spectrumero/filestick/system/console.c

/*
;The MIT License
;
;Copyright (c) 2023 Dylan Smith
;
;Permission is hereby granted, free of charge, to any person obtaining a copy
;of this software and associated documentation files (the "Software"), to deal
;in the Software without restriction, including without limitation the rights
;to use, copy, modify, merge, publish, distribute, sublicense, and/or sell
;copies of the Software, and to permit persons to whom the Software is
;furnished to do so, subject to the following conditions:
;
;The above copyright notice and this permission notice shall be included in
;all copies or substantial portions of the Software.
;
;THE SOFTWARE IS PROVIDED "AS IS", WITHOUT WARRANTY OF ANY KIND, EXPRESS OR
;IMPLIED, INCLUDING BUT NOT LIMITED TO THE WARRANTIES OF MERCHANTABILITY,
;FITNESS FOR A PARTICULAR PURPOSE AND NONINFRINGEMENT. IN NO EVENT SHALL THE
;AUTHORS OR COPYRIGHT HOLDERS BE LIABLE FOR ANY CLAIM, DAMAGES OR OTHER
;LIABILITY, WHETHER IN AN ACTION OF CONTRACT, TORT OR OTHERWISE, ARISING FROM,
;OUT OF OR IN CONNECTION WITH THE SOFTWARE OR THE USE OR OTHER DEALINGS IN
;THE SOFTWARE.
*/

#include <stdint.h>
#include <stdbool.h>
#include <unistd.h>
#include <sys/stat.h>
#include <string.h>
#include <sys/errno.h>

#include "sys/console.h"
#include "console.h"
#include "fd.h"
#include "sysdefs.h"
#include "devices.h"

static FDfunction cons_func = {
   .fd_read  = console_read,
   .fd_write = console_write,
   .fd_lseek = NULL,
   .fd_fstat = console_fstat,
   .fd_close = NULL,
   .fd_ioctl = console_ioctl,
   .fd_peek  = console_peek
};

#ifdef SOFTWARE_FIFO
extern volatile uint32_t bufindex;
extern volatile uint32_t bufstart;
extern volatile uint32_t cr_index;
extern volatile uint32_t cons_rx_count;
extern volatile uint32_t cons_control;

// This should be able to pick up the symbol, but it doesn't
uint8_t *cons_buf = (uint8_t *)0xff00; // FIXME system.ld symbol
#else
uint32_t       cons_control;
#endif

static ssize_t console_read_interactive(int fd, void *buf, size_t count);
static ssize_t console_read_raw(int fd, void *buf, size_t count);

//------------------------------------------------------------------
// Open the console
int open_console(const char *devname, int flags, mode_t mode, FD *fd) {
   fd->fdfunc = &cons_func;
   return 0;
}

//-----------------------------------------------------------------
// Read the console
ssize_t console_read(int fd, void *buf, size_t count) {
   if(cons_control & CONSOLE_RAW) 
      return console_read_raw(fd, buf, count);
   else 
      return console_read_interactive(fd, buf, count);
}

#ifdef SOFTWARE_FIFO
//-----------------------------------------------------------------
// Read the console in raw mode
static ssize_t console_read_raw(int fd, void *buf, size_t count)
{
   size_t bytes_remain = count;
   uint8_t *bufptr = (uint8_t *)buf;
   bool do_flow_control = false;

   if(!count) return 0;

   while(bytes_remain) {
      while(bufstart != bufindex && bytes_remain) {
         uint8_t byte = *(cons_buf + (bufstart & 0xFF));
         *bufptr++ = byte;

         bufstart++;
         bytes_remain--;
         do_flow_control = true;
      }

      if(do_flow_control) {
         if(cons_control & CONSOLE_FLOW_XOFF)
            serial_putc(FLOW_XON);

         do_flow_control = false;
      }
   }

   return count;
}

//-----------------------------------------------------------------
// Read the console in interactive mode (characters echoed, CR = end
// of transmission)
static ssize_t console_read_interactive(int fd, void *buf, size_t count)
{
   size_t bytes_read = 0;
   uint8_t *bufptr = (uint8_t *)buf;

   if(!count) return 0;

   // FIXME will need a way to break out (eg Ctrl-C)
   while(cons_rx_count == 0);

   DISABLE_INTERRUPTS
   cons_rx_count--;
   ENABLE_INTERRUPTS

   while(count && bufstart != bufindex) {
      // add the wrapped value of bufstart to get the buffer index
      uint8_t byte = *(cons_buf + (bufstart & 0xFF));
      *bufptr++ = byte;

      bufstart++;
      count--;
      bytes_read++;

   }

   return bytes_read;
}
#else // SOFTWARE_FIFO

// Using the hardware FIFO
volatile uint8_t  *uart_byte  = (uint8_t *)(DEV_BASE + OFFS_UART);
volatile uint32_t *uart_state = (uint32_t *)(DEV_BASE + OFFS_UARTSTATE);

//-----------------------------------------------------------------
// Read the console in raw mode
static ssize_t console_read_raw(int fd, void *buf, size_t count)
{
   uint8_t *bufptr = buf;
   ssize_t bytes_read = 0;

   while(count) {
      // wait for data
      while((*uart_state & 1) == 0);

      uint8_t byte = *uart_byte;
      *bufptr++ = byte;
      count--;
      bytes_read++;
   }
      
   return bytes_read;
}

//-----------------------------------------------------------------
// Read the console in interactive mode (characters echoed, CR = end
// of transmission)
static ssize_t console_read_interactive(int fd, void *buf, size_t count)
{
   size_t bytes_read = 0;
   uint8_t *bufptr = buf;
   if(count == 0) return 0;

   while(count) {
      // wait for data
      while((*uart_state & 1) == 0);

      uint8_t byte = *uart_byte;

      // CR
      if(byte == 0x0d) {
         serial_putc(0x0a);
         serial_putc(0x0d);
         break;
      }
      // backspace
      else if(byte == 127 || byte == 8) {
         if(bufptr > (uint8_t *)buf) {
            bufptr--;
            *bufptr = 0;
            bytes_read--;
            count++;
            serial_putc(8);
            serial_putc(' ');
            serial_putc(8);
         }
         else {
            // bell
            serial_putc(7);
         }
      }
      else {
         serial_putc(byte);
         count--;
         bytes_read++;
         *bufptr++ = byte;
      }
   }

   return bytes_read;
}
#endif

//------------------------------------------------------------------
// Return the number of bytes available
ssize_t console_peek(int fd) {
#ifdef SOFTWARE_FIFO
   return bufindex - bufstart;
#else
   // FIFO remaining bytes are in the upper 16 bits of the state
   // register
   return (*uart_state) >> 16;
#endif
}

//------------------------------------------------------------------
// Write to the system console.
ssize_t console_write(int fd, const void *buf, size_t count) {
   ssize_t rc = count;
   char *bufptr = (char *)buf;

   while(count--) {
      if(cons_control & CONSOLE_RAW)
         raw_putc(*bufptr++);
      else
         serial_putc(*bufptr++);
   }

   return rc;
}

//------------------------------------------------------------------
// stat the console
int console_fstat(int fd, struct stat *statbuf) {
   memset(statbuf, 0, sizeof(struct stat));
   statbuf->st_mode = S_IFCHR | 0777;
   statbuf->st_nlink = 1;
   return 0;
}

//------------------------------------------------------------------
// console ioctl
int console_ioctl(int fd, unsigned long request, void *ptr) {
   uint32_t req_id = request & 0xFF000000;

   switch(req_id) {
      case CONSOLE_SET_CONTROL:
         cons_control = request & 0xFFFF;
         break;
      case CONSOLE_SET_RAW:
         cons_control |= CONSOLE_RAW;
         break;
      case CONSOLE_SET_INTERACTIVE:
         cons_control &= CONSOLE_CLR_RAW;
         break;
#ifdef SOFTWARE_FIFO
      case CONSOLE_DISCARD_RXBUF:
         bufstart = bufindex;
         break;
#endif
      default:
         return -EINVAL;
   }
   return 0;
}
